NicheElectronics/USB-to-I2C-CONVERTER/validation/ft-prog/FTProg-CBUS5-CLK24MHz-Configuration.png

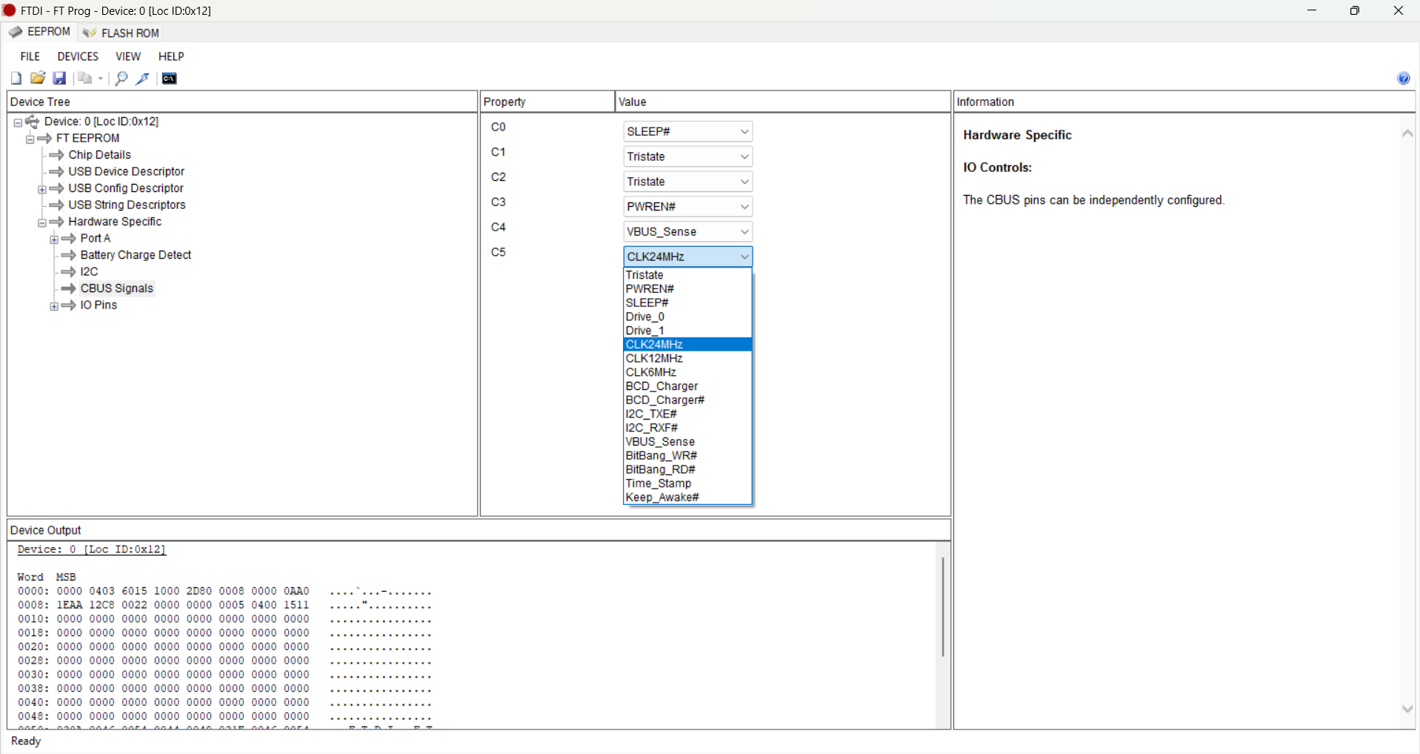
validation/ft-prog/FTProg-CBUS5-CLK24MHz-Configuration.png
