NicheElectronics/USB-to-I2C-CONVERTER/validation/ft-prog/FTProg-FT201X-Device-Detected.png

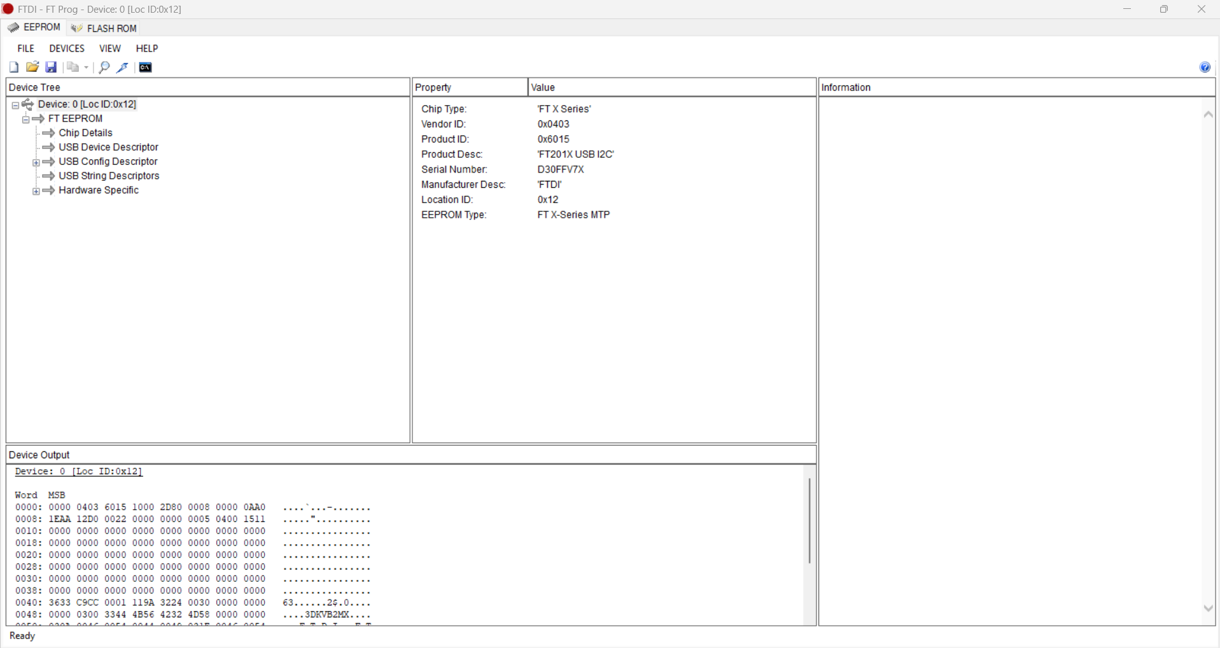
validation/ft-prog/FTProg-FT201X-Device-Detected.png
